pingringme/doorbell-watcher/simulation/voltage_input.asc

C1: cap; {Cin}
Cin: polcap; {Cin}; V=25 Irms=1.27 Rser=0.055 Lser=0
Cout: polcap; 220µ; V=16 Irms=460m Rser=0.16 Lser=0 mfg="Nichicon" pn="UPL1C221MPH" type="Al electrolytic"
D1: schottky; 1N5824
D2: diode; 1N4148
D3: diode; 1N4148
D4: diode; 1N4148
D5: diode; 1N4148
L1: ind; 100µ; Ipk=3 Rser=50m Cpar=0
RLOAD: res; {RL}
U1: LM2596xx; LM2596_05
V1: voltage; SINE(0 {Vp} 50)
Named nets: OUTPUT, +VIN, OUT, Vp, Vn, 0
.tran 0 200m 140m startup
.ic I(L1)=0
.inc LM2596xx.txt
.options plotwinsize=0
.param Vac=12 Vp={Vac*1.41}
.param VOut=5
.param IOut=250m
.param RL={VOut/IOUT}
.meas RLx param RL
.inc 1n582x.txt
UNREGULATED
DC INPUT
REGULATED OUTPUT
.param Cin=340u
