pingringme/doorbell-watcher/simulation/button_signal.asc

C1: cap; 100n
D5: diode
D6: diode
D7: diode
D8: diode
Digital_Input: res; 1Meg
R1: res; 330R
R2: res; 50k
R3: res; 330
R4: res; 250
S1: sw; BUTTON
SwitchControl: voltage; SINE(0 5 .5)
U1: PC817A
U2: PC817A
V1: voltage; SINE(0 34 50)
V2: voltage; 3.3
Named nets: Vin1, C1, Vin2, 0, 3V3
.tran 0 5s 0
.model BUTTON SW(Ron=1 Roff=1Meg Vt=.5 Vh=-.4)
